CircuitGuy943/Recept-5GHz-FPV-Reciever/Pictures/Finish/3dmodel.png

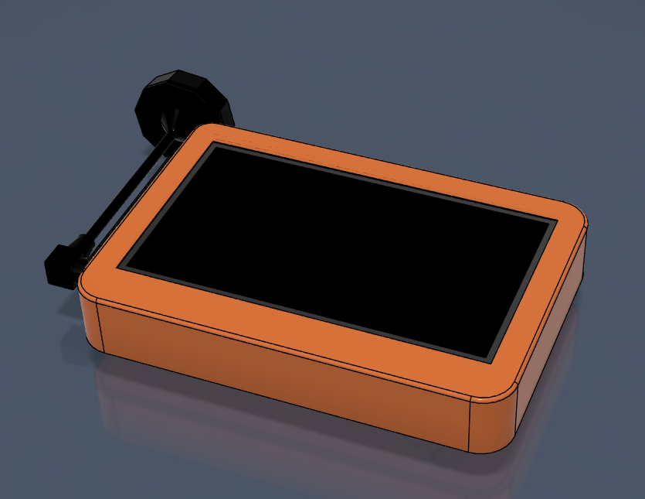
Pictures/Finish/3dmodel.png
