CircuitGuy943/Recept-5GHz-FPV-Reciever/Pictures/Finish/PCB_L1234.png

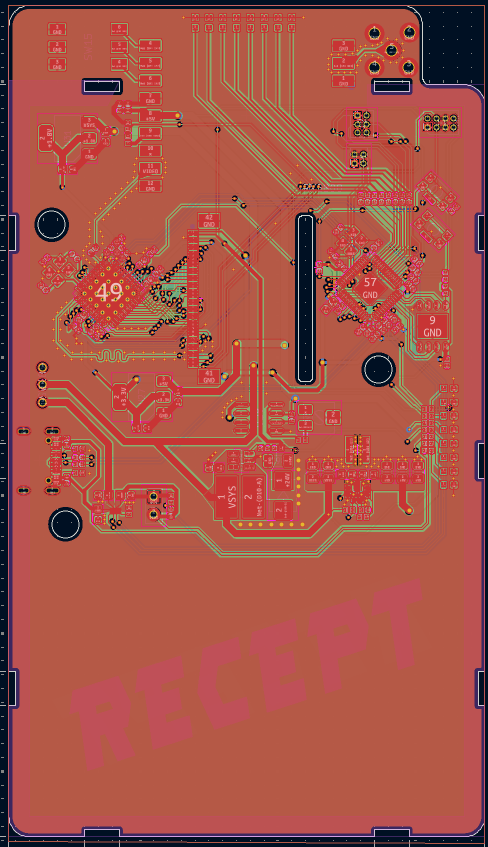
Pictures/Finish/PCB_L1234.png
