CircuitGuy943/Recept-5GHz-FPV-Reciever/Pictures/JLCPCB Basket.png

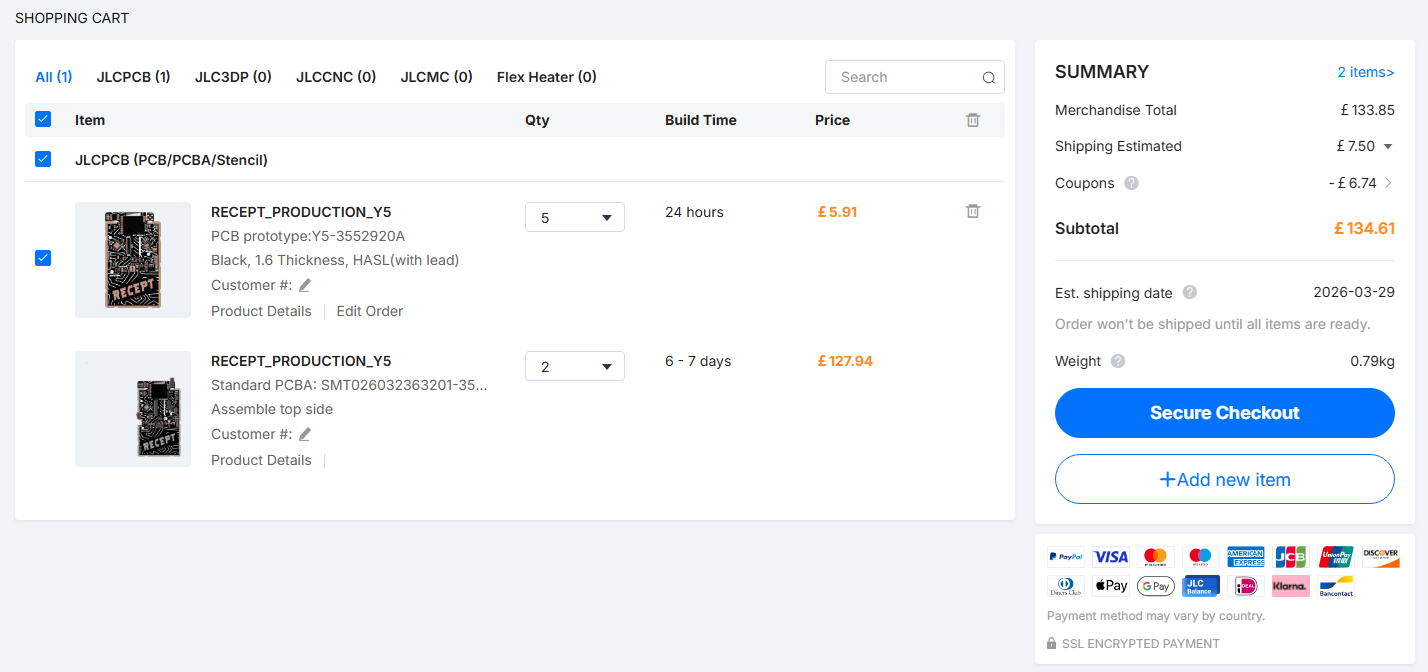
Pictures/JLCPCB Basket.png
