CircuitGuy943/Recept-5GHz-FPV-Reciever/Pictures/Renders/render2transparent.png

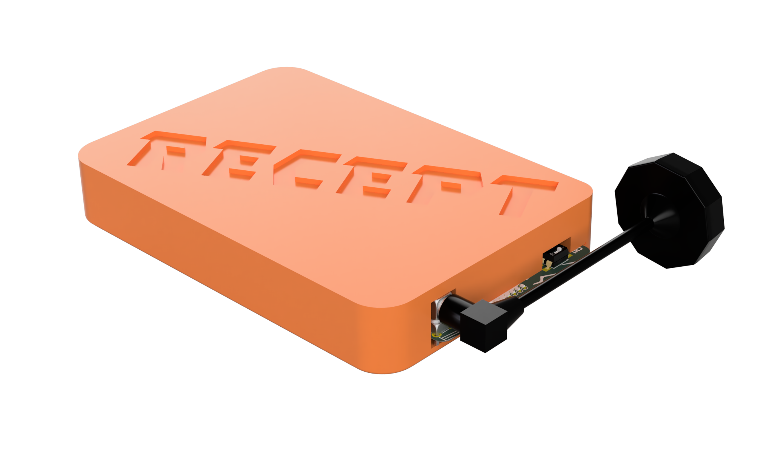
Pictures/Renders/render2transparent.png
