CircuitGuy943/Recept-5GHz-FPV-Reciever/Pictures/Renders/render3transparent.png

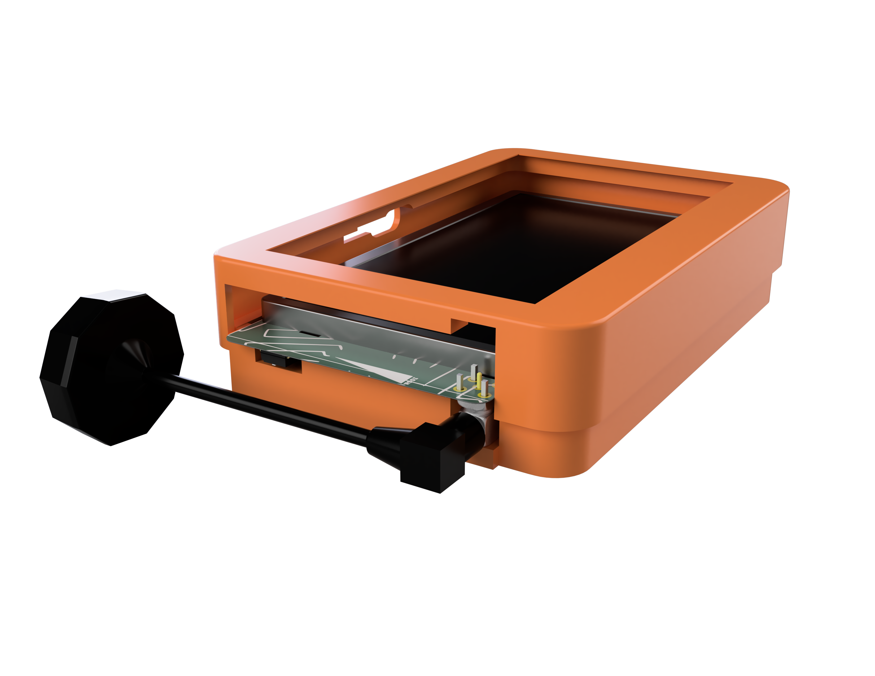
Pictures/Renders/render3transparent.png
