CircuitGuy943/Recept-5GHz-FPV-Reciever/Pictures/Renders/render8transparent.png

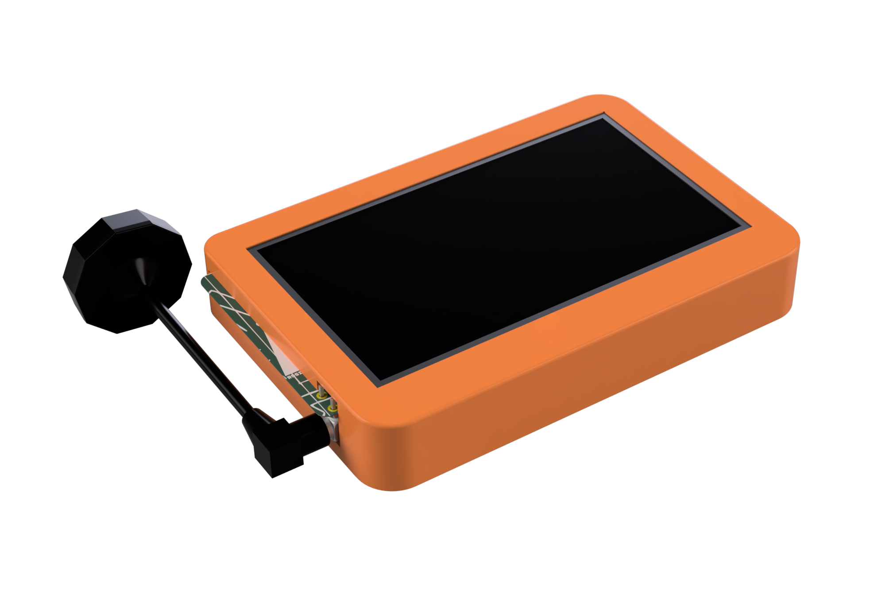
Pictures/Renders/render8transparent.png
